jean-claudeF/SolarPower/Overcharge_and_discharge_protection_for_battery_01.sch

## KiCad design Overcharge_and_discharge_protection_for_battery_01.sch (2023-06-04)

Schematic: Overcharge_and_discharge_protection_for_battery_01.sch

Parts:
D1, D2, D9, D10: ZD8v2; D_SMF
D3, D11: LED
D4: ZD30; D_SMF
D5, D6, D12: 1N4148
D7, D8: ZD18; D_SMF
J1: Charging power
J2: Battery
J3: Load
Q1, Q2, Q5, Q6, Q7: BC546
Q3, Q4: SUP90P06-09L
R1: 120k
R2, R4, R16, R18: 22k
R3, R7, R17, R20, R23, R27: 10k
R5: 15k
R6: 56k
R8, R19: 1k
R9, R21: 2M2
R10, R15, R22, R24, R25: 100k
R11, R12, R13, R14: 47k
R26: 27k
R28, R29: 0.01
RV1, RV2: 10k
U1, U2: TL081

Notes on the sheet:
Level
Hysteresis
LED CHARGE OK
+30V Supply for control circuit
H = Charge OK
L = Discharge OK
H = Discharge OK
Overcharge protection
Discharge protection
LED Discharge OK
14.3.2023
