jean-claudeF/SolarPower/UmschaltungSolarNetz.sch

## KiCad design UmschaltungSolarNetz.sch (2023-06-04)

Schematic: UmschaltungSolarNetz.sch

Parts:
C1: 0.56uF
D1: D
J1: Socket 2x 230V
K1: AZ850-x; Relay_DPDT_FRT5
MES1: Amperemeter_AC
MES2: Voltmeter_DC
NE1: Lamp_Neon
P1: Grid 230V
P2: Solar 230V
R1: (no value)
R2: R
SW1: Solar ON

Notes on the sheet:
R2 für korrekte Anzeige des Effektivwertes.
K1 = Schütz AEG 55E (recycelt)
Schütz schaltet auf Solarnetz wenn Solarnetz Spannung hat und SW1 eingeschaltet ist
Anzeige Solarnetz
Eingang Solarnetz
Eingang Hausnetz
Ausgang 230V
