jean-claudeF/SolarPower/measure_UII_HA.sch

## KiCad design measure_UII_HA.sch (2023-06-04)

Schematic: measure_UII_HA.sch

Parts:
C1: 4u7
C2, C3, C4, C5: 100n
D1, D2: ZD18; D_SMF
D3, D4: D
J1: Charging power
J2: Battery
J3: Load
Q1, Q2: SUP90P06-09L
R1: Rs1
R2: Rs2
R3: 47k
R4: 2k7
R5, R11, R12, R13, R14: 10k
R6: 1M
R7: 1k
R8: 100k
R9, R10: 18k
R15, R16: 10K
SW1: SW1
U1, U2: TLC2652
U3: SH1106
U4: ADS1115IDGS; TSSOP-10_3x3mm_P0.5mm
W1: D1mini

Notes on the sheet:
Discharge current shunt
Charge current shunt
Voltage signal
Load current signal
Charge current signal
ADDR = 0x48
ADDR = 0x3C
D5, D6,D7 INPUT with pullup
(Don't use D8 as input with pullup!)
