jean-claudeF/SolarPower/KiCAD/MPPT_03.sch

## KiCad design KiCAD/MPPT_03.sch (2023-09-25)

Schematic: MPPT_03.sch

Parts:
C1, C2: 100nF
C3: 47uF
C4, C5: 200uF
D1, D2: ZD27; D_SMF
D3: D_Schottky
J7, J8: (no value)
JP1: Auto / Manual PWM
L1: 150uH
Q1: BC547
Q2, Q3: IRFP4368
R1, R7: 1k
R2: 4k7
R3: 10k
R4: 12
R5: 10m
R6: 20k
R8: Rshunt
R9: Rout
RV1: 10k
U1: IR2101
U3: INA169; SOT-23-5
U6: SH1106
U7: Pico; RPi_Pico_SMD_TH

Notes on the sheet:
I2C SCL
I2C SDA
I2C pullups on breakout boards
Rshunt = 10mOhm Rout = 10k (is already on breakout board) for 30A range
Solar stepup converter
OUTPUT To battery overcharge protection circuit
Manual PWM (only when JP1 is set) RV1 can be omitted when JP1 is not set.
JP1 set: Manual PWM over Rv1 JP1 open: Automatic MPP tracking
PWM
Idle state protection
From solar panels + 10-40V
+5V from Battery power over DC-DC converter
