jean-claudeF/SolarPower/KiCAD/MPPT_05_2B_controlcircuit.kicad_sch

## KiCad design KiCAD/MPPT_05_2B_controlcircuit.kicad_sch (2025-07-26)

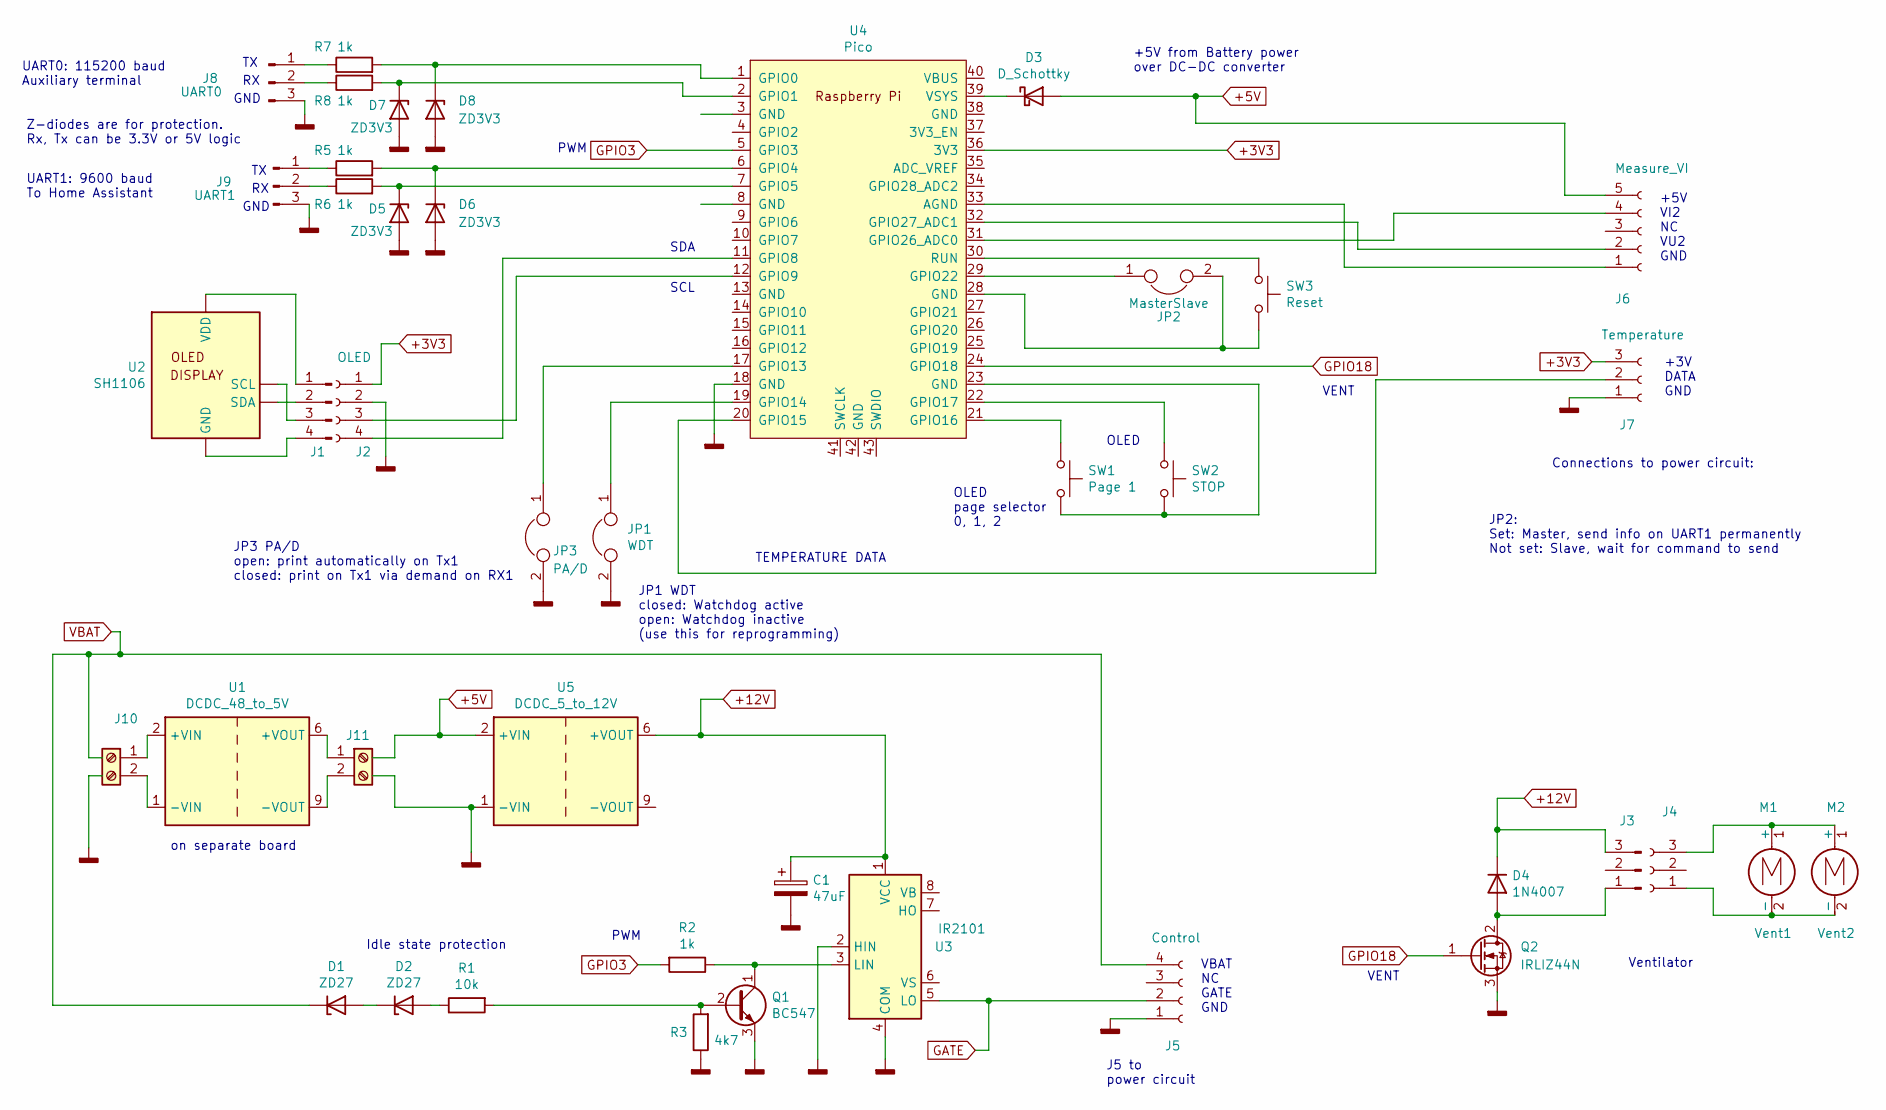
[picture p47: schematic MPPT_05_2B_controlcircuit.kicad_sch]

Parts:
C1: 47uF
D1, D2: ZD27; D_SMF
D3: D_Schottky
D4: 1N4007; D_DO-41_SOD81_P10.16mm_Horizontal
D5, D6, D7, D8: ZD3V3
J1, J3, J4, J10, J11: (no value)
J2: OLED
J5: Control
J6: Measure_VI
J7: Temperature
J8: UART0
J9: UART1
JP1: WDT
JP2: MasterSlave
JP3: PA/D
M1: Vent1
M2: Vent2
Q1: BC547
Q2: IRLIZ44N; TO-220F-3_Vertical
R1: 10k
R2, R5, R6, R7, R8: 1k
R3: 4k7
SW1: Page 1
SW2: STOP
SW3: Reset
U1: DCDC_48_to_5V; Converter_DCDC_TRACO_TMR-2xxxxWI_THT
U2: SH1106
U3: IR2101
U4: Pico; RPi_Pico_SMD_TH
U5: DCDC_5_to_12V; Converter_DCDC_TRACO_TMR-2xxxxWI_THT

Connections:
+3V3: J2.1, J7.3, U4.36 (3V3)
+5V: D3.2 (A), J6.5, U5.2 (+VIN)
+12V: C1.1, D4.1 (K), J3.3, U3.1 (VCC), U5.6 (+VOUT)
GATE: J5.2, U3.5 (LO)
GNDD: C1.2, D5.2 (A), D6.2 (A), D7.2 (A), D8.2 (A), J2.2, J5.1, J7.1, J8.3, J9.3, JP1.2, JP3.2, Q1.3 (E), Q2.3 (S), R3.1, U3.2 (HIN), U3.4 (COM), U4.18 (GND), U5.1 (-VIN)
GPIO3: R2.2, U4.5 (GPIO3)
GPIO18: Q2.1 (G), U4.24 (GPIO18)
unnamed: D1.2 (A), D2.1 (K)
unnamed: D2.2 (A), R1.1
unnamed: D3.1 (K), U4.39 (VSYS)
unnamed: D4.2 (A), J3.1, Q2.2 (D)
unnamed: D5.1 (K), R6.2, U4.7 (GPIO5)
unnamed: D6.1 (K), R5.2, U4.6 (GPIO4)
unnamed: D7.1 (K), R8.2, U4.2 (GPIO1)
unnamed: D8.1 (K), R7.2, U4.1 (GPIO0)
unnamed: J1.1, U2.8 (VDD)
unnamed: J1.2, U2.9 (SDA)
unnamed: J1.3, U2.10 (SCL)
unnamed: J1.4, U2.3 (GND)
unnamed: J2.3, U4.12 (GPIO9)
unnamed: J2.4, U4.11 (GPIO8)
unnamed: J4.1, M1.2 (-), M2.2 (-)
unnamed: J4.3, M1.1 (+), M2.1 (+)
unnamed: J6.1, U4.33 (AGND)
unnamed: J6.2, U4.32 (GPIO27_ADC1)
unnamed: J6.4, U4.31 (GPIO26_ADC0)
unnamed: J7.2, U4.20 (GPIO15)
unnamed: J8.1, R7.1
unnamed: J8.2, R8.1
unnamed: J9.1, R5.1
unnamed: J9.2, R6.1
unnamed: J10.1, U1.2 (+VIN)
unnamed: J10.2, U1.1 (-VIN)
unnamed: J11.1, U1.6 (+VOUT)
unnamed: J11.2, U1.9 (-VOUT)
unnamed: JP1.1, U4.19 (GPIO14)
unnamed: JP2.1, U4.29 (GPIO22)
unnamed: JP2.2, SW3.2, U4.28 (GND)
unnamed: JP3.1, U4.17 (GPIO13)
unnamed: Q1.1 (C), R2.1, U3.3 (LIN)
unnamed: Q1.2 (B), R1.2, R3.2
unnamed: SW1.1, U4.21 (GPIO16)
unnamed: SW1.2, SW2.2, U4.23 (GND)
unnamed: SW2.1, U4.22 (GPIO17)
unnamed: SW3.1, U4.30 (RUN)
VBAT: D1.1 (K), J5.4

Notes on the sheet:
J5 to power circuit
+3V DATA GND
Z-diodes are for protection. Rx, Tx can be 3.3V or 5V logic
JP1 WDT closed: Watchdog active open: Watchdog inactive (use this for reprogramming)
TEMPERATURE DATA
UART1: 9600 baud To Home Assistant
GND
PWM
VENT
Connections to power circuit:
JP3 PA/D open: print automatically on Tx1 closed: print on Tx1 via demand on RX1
JP2: Set: Master, send info on UART1 permanently Not set: Slave, wait for command to send
SDA
+5V from Battery power over DC-DC converter
OLED
SCL
Idle state protection
UART0: 115200 baud Auxiliary terminal
Ventilator
on separate board
+5V VI2 NC VU2 GND
OLED page selector 0, 1, 2
VBAT NC GATE GND
