jean-claudeF/SolarPower/KiCAD/MPPT_05_2B_powercircuit.kicad_sch

## KiCad design KiCAD/MPPT_05_2B_powercircuit.kicad_sch (2025-07-26)

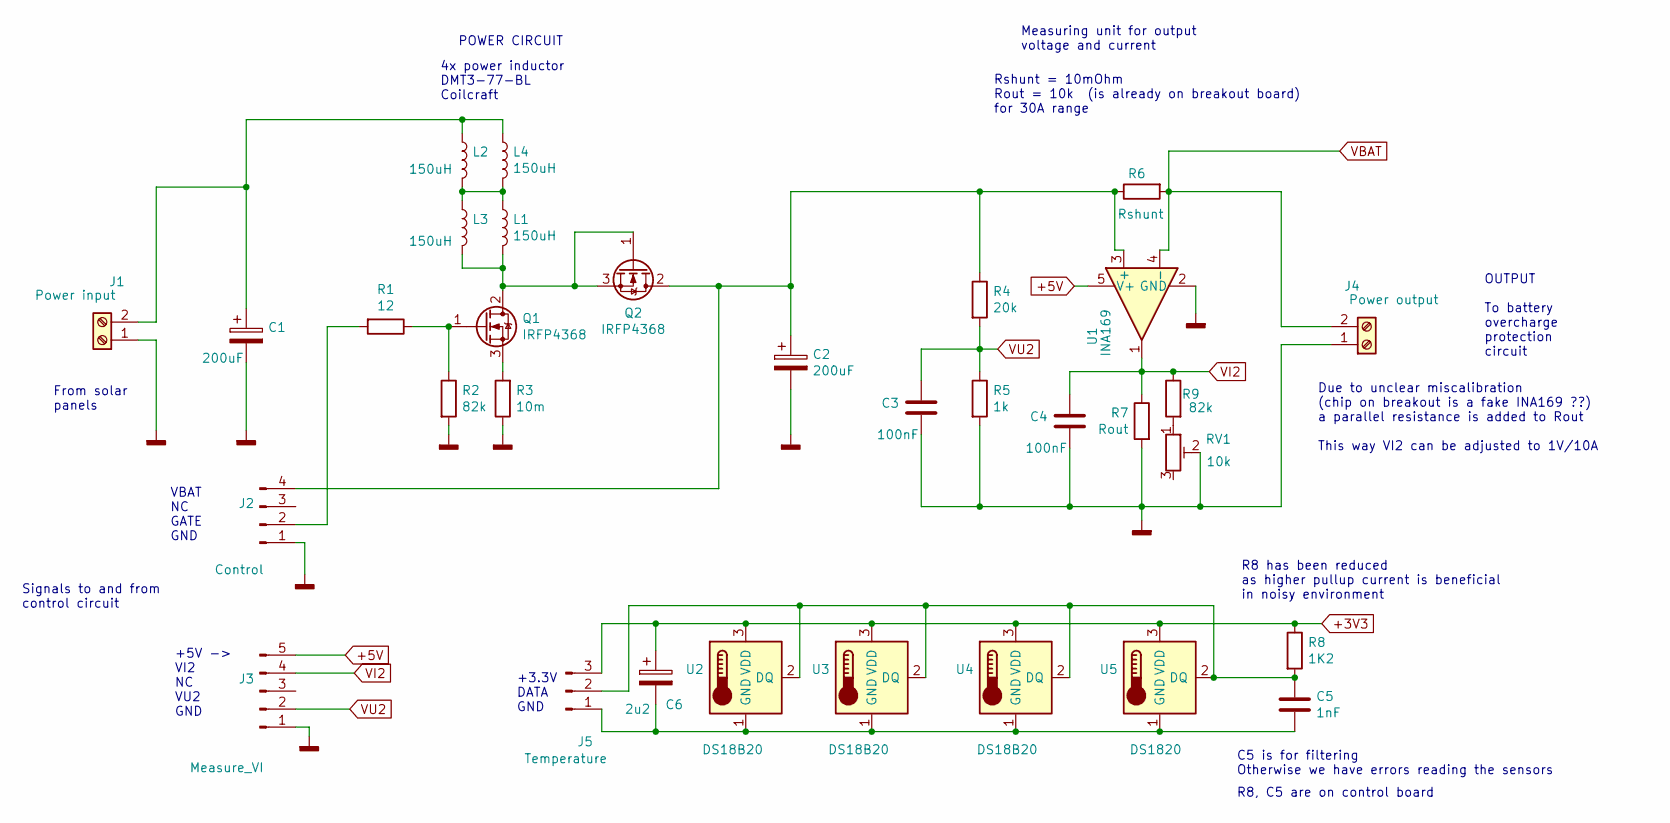
[picture p48: schematic MPPT_05_2B_powercircuit.kicad_sch]

Parts:
C1, C2: 200uF
C3, C4: 100nF
C5: 1nF
C6: 2u2
J1: Power input
J2: Control
J3: Measure_VI
J4: Power output
J5: Temperature
L1, L2, L3, L4: 150uH
Q1, Q2: IRFP4368
R1: 12
R2, R9: 82k
R3: 10m
R4: 20k
R5: 1k
R6: Rshunt
R7: Rout
R8: 1K2
RV1: 10k
U1: INA169; SOT-23-5
U2, U3, U4: DS18B20; TO-92_Inline
U5: DS1820; TO-92_Inline

Connections:
+3V3: C6.1, J5.3, R8.1, U2.3 (VDD), U3.3 (VDD), U4.3 (VDD), U5.3 (VDD)
+5V: J3.5, U1.5 (V+)
GNDD: C1.2, C2.2, C3.2, C4.2, J1.1, J2.1, J3.1, J4.1, R2.2, R3.1, R5.2, R7.2, RV1.2, U1.2 (GND)
unnamed: C1.1, J1.2, L2.1, L4.1
unnamed: C2.1, J2.4, Q2.2 (D), R4.1, R6.1, U1.3 (+)
unnamed: C5.1, J5.2, R8.2, U2.2 (DQ), U3.2 (DQ), U4.2 (DQ), U5.2 (DQ)
unnamed: C5.2, C6.2, J5.1, U2.1 (GND), U3.1 (GND), U4.1 (GND), U5.1 (GND)
unnamed: J2.2, R1.2
unnamed: L1.1, L2.2, L3.1, L4.2
unnamed: L1.2, L3.2, Q1.2 (D), Q2.1 (G), Q2.3 (S)
unnamed: Q1.1 (G), R1.1, R2.1
unnamed: Q1.3 (S), R3.2
unnamed: R9.2, RV1.1
VBAT: J4.2, R6.2, U1.4 (-)
VI2: C4.1, J3.4, R7.1, R9.1, U1.1
VU2: C3.1, J3.2, R4.2, R5.1

Notes on the sheet:
From solar panels
POWER CIRCUIT
Measuring unit for output voltage and current
VBAT NC GATE GND
Rshunt = 10mOhm Rout = 10k (is already on breakout board) for 30A range
+5V -> VI2 NC VU2 GND
+3.3V DATA GND
OUTPUT To battery overcharge protection circuit
R8, C5 are on control board
Signals to and from control circuit
Due to unclear miscalibration (chip on breakout is a fake INA169 ??) a parallel resistance is added to Rout This way VI2 can be adjusted to 1V/10A
4x power inductor DMT3-77-BL Coilcraft
R8 has been reduced as higher pullup current is beneficial in noisy environment
C5 is for filtering Otherwise we have errors reading the sensors
